calinemanuelsebastian/portable-hurricane-weather-station/images/IMG_7052-1.jpg

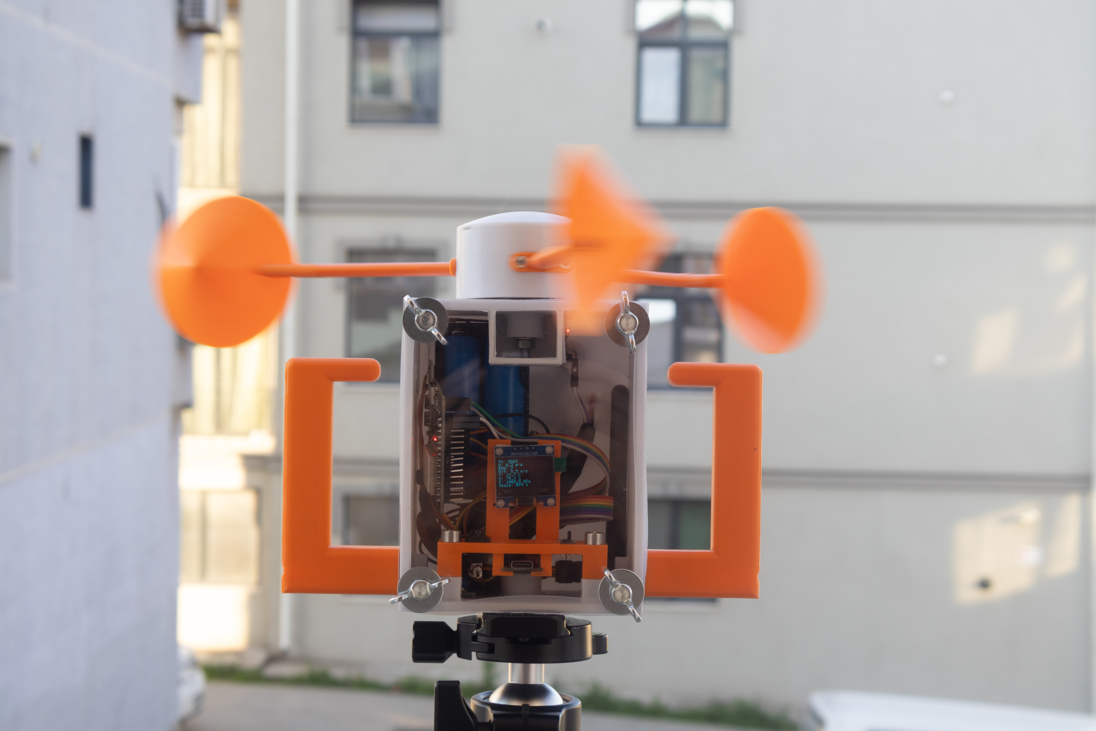
images/IMG_7052-1.jpg
