calinemanuelsebastian/portable-hurricane-weather-station/images/IMG_7053-2.jpg

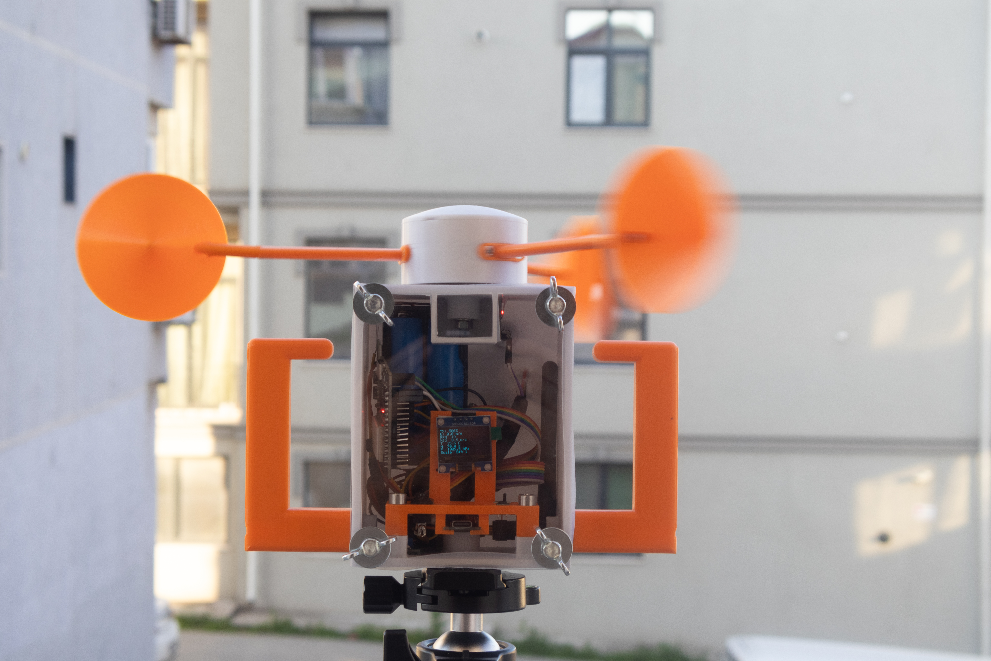
images/IMG_7053-2.jpg
